JBeeBK/USB_C_PD/00_Hardware/Project_Footprints/nRF52840-QFAA-F-R7.stp

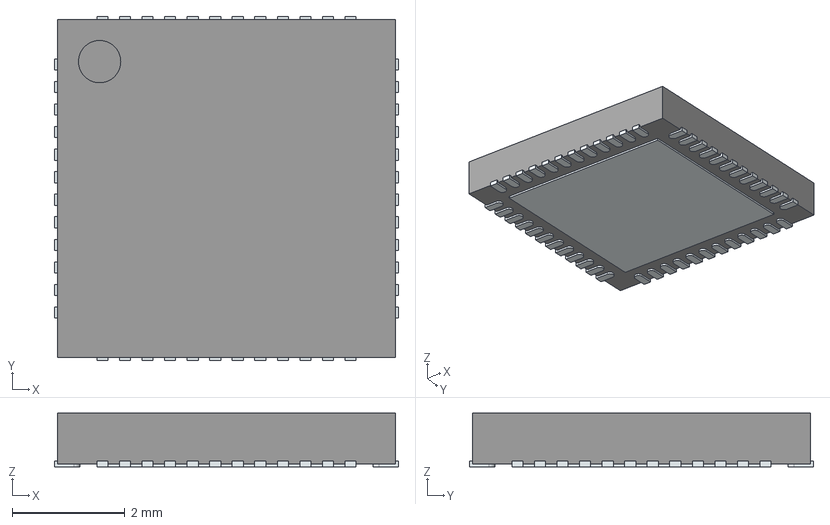
[picture p16: CAD file, 2025-07-25]
00_Hardware/Project_Footprints/nRF52840-QFAA-F-R7.stp
6.10 x 6.10 x 0.95 mm
ThermalPin
PinsArrayLR
PinsArrayTB
